4n3m4i1/Bode_Analyzer/App/FletApp/assets/Ari.png

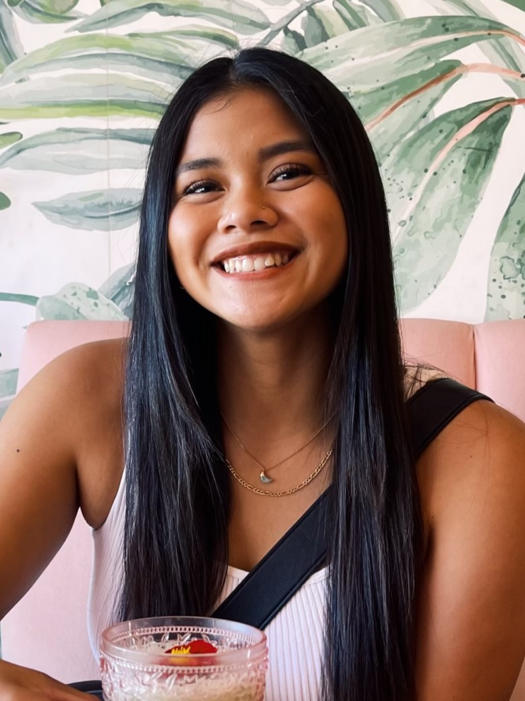
App/FletApp/assets/Ari.png
