4n3m4i1/Bode_Analyzer/App/FletApp/assets/AriBBTwo.png

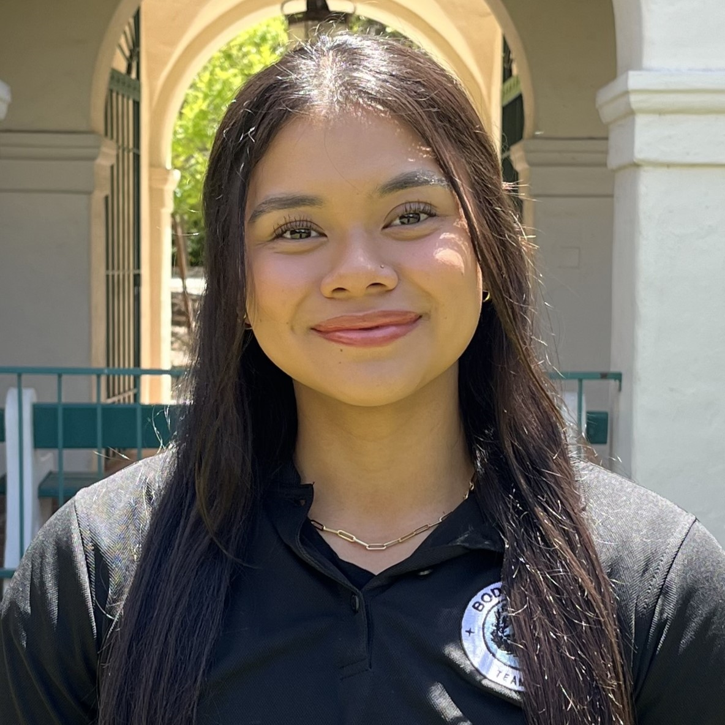
App/FletApp/assets/AriBBTwo.png
