4n3m4i1/Bode_Analyzer/App/FletApp/assets/ChristianFriends.png

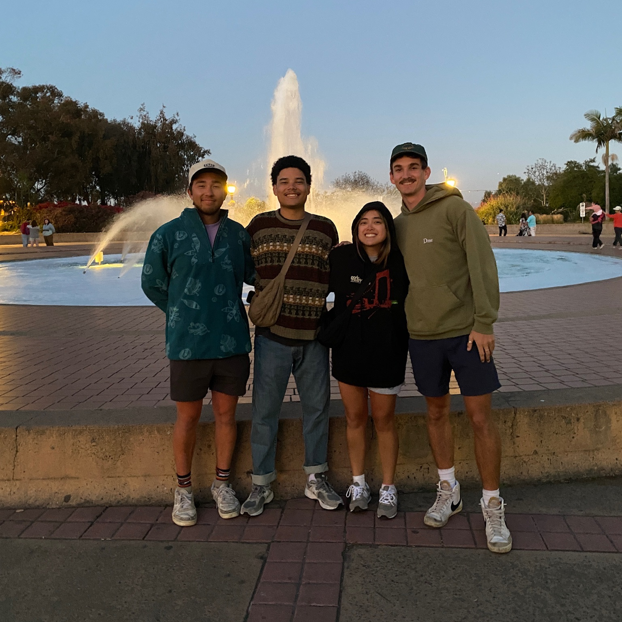
App/FletApp/assets/ChristianFriends.png
