4n3m4i1/Bode_Analyzer/App/FletApp/assets/JoshHobby.png

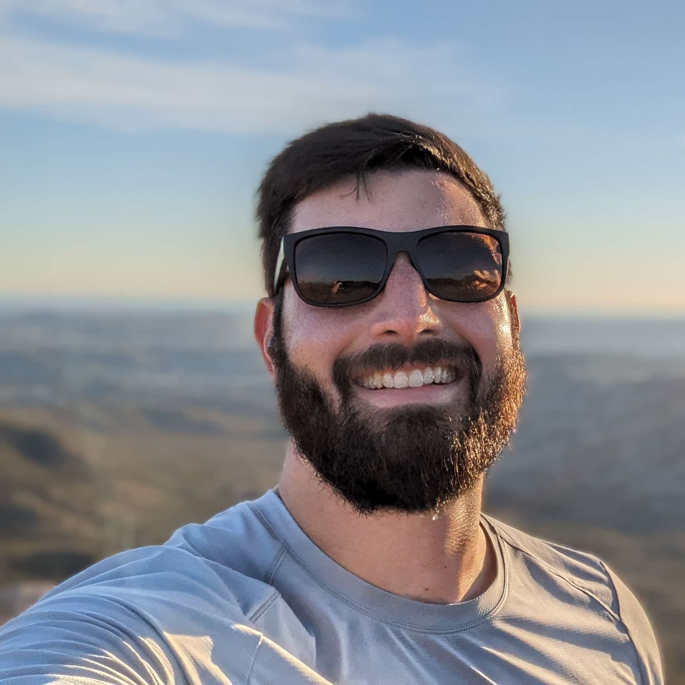
App/FletApp/assets/JoshHobby.png
