4n3m4i1/Bode_Analyzer/img/Ari.png

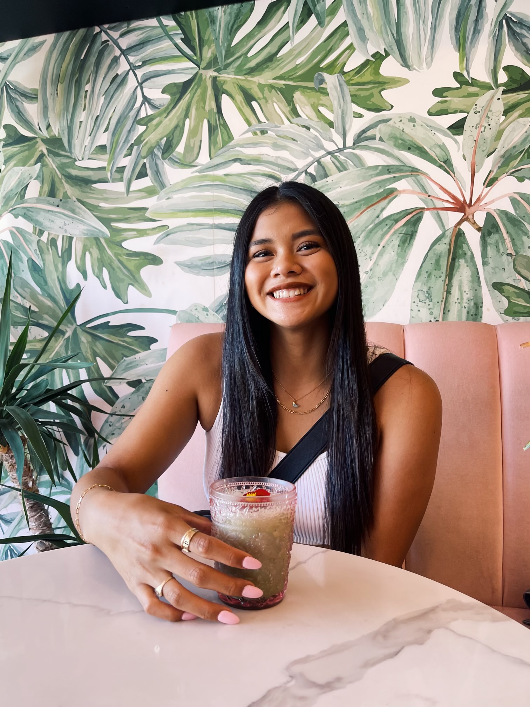
img/Ari.png
