4n3m4i1/Bode_Analyzer/Documentation/DSP/AdaptiveFilter/C_Adaptive_Filter_Test_Var_Taps/main.c

#include <stdio.h>
#include <stdlib.h>
#include <malloc.h>
#include <inttypes.h>
#include <math.h>

#define LIMIT_FOR_ERROR     1.0

#define DFL_ITERATIONS      256

#define DFL_BETA_RATE       0.005

#define ERR_AVE_LEN         8

uint32_t    print_options = 0;
#define CSV_OI4V_FMT        1u
#define TGT_VIDEO_FRAMES    1000

#define STARTING_TAP_TGT    32
#define MAX_TAP_TGT         1024

uint32_t    ideal_tap_num = 0;
uint32_t    adaptive_tap_num = 1024;
uint32_t    iterations = DFL_ITERATIONS;

// Different algorithms for H_HAT updates, leave all commented for DFL
//#define HALG_2        // DOESN'T WORK!!!!
//#define HALG_3        // DOESN'T WORK EVEN W /0 FIX!!
//#define HALG_4        // kinda a joke to try this one
//#define HALG_5

// Sorta kinda Box-Muller + Lazy Programming
double generate_awgn_sample(){
    double U1 = drand48();

    return sqrt(-2 * log(U1)) - 1.25;
}


// Simulate a DUT response HERE
double perform_fir(double *ideal_taps, double *idt_delay_line, double new_value, uint32_t len){
    double retval = 0;
    if(ideal_taps && idt_delay_line){
        idt_delay_line[0] = new_value;
        for(uint32_t n = 0; n < len; ++n) retval += ideal_taps[n] * idt_delay_line[n];
        for(uint32_t n = len - 1; n > 0; --n) idt_delay_line[n] = idt_delay_line[n - 1];
    }
    return retval;
}


void update_h_hat(double *h_hat_taps, double *idt_delay_line, double error, double beta_rate, uint32_t len){
    if(h_hat_taps && idt_delay_line){
#ifdef HALG_2
        for(uint32_t n = 0; n < len - 1; ++n){
            h_hat_taps[n + 1] = h_hat_taps[n] + beta_rate * (error * idt_delay_line[n]);
        }
#elif defined(HALG_3)
// Normalized
        for(uint32_t n = 0; n < len; ++n){
            if(!idt_delay_line[n]) idt_delay_line[n] += 1e-12;
            h_hat_taps[n] += (beta_rate * error) / (idt_delay_line[n]);
            printf("HE %lf\n",h_hat_taps[n]);
        }
#elif defined(HALG_4)
        for(uint32_t n = 0; n < len; ++n){
            h_hat_taps[n] -= beta_rate * (error * idt_delay_line[n]);
        }
#elif defined(HALG_5)
        for(uint32_t n = 0; n < len; ++n){
            h_hat_taps[n] += beta_rate * (2.0 * error * idt_delay_line[n]);
        }
#else
        for(uint32_t n = 0; n < len; ++n){
            h_hat_taps[n] += beta_rate * (error * idt_delay_line[n]);
        }
#endif
    }
}


void main(int argc, char **argv){
    if(argc > 1){
        iterations = strtoul(argv[1],NULL,10);
    }
    printf("Running %u samples of white noise through the system!\n", iterations);

    double beta = DFL_BETA_RATE;

    if(argc > 2){
        beta = strtod(argv[2],NULL);
    }

    printf("Beta adaptive rate: %lf\n",beta);


    FILE *printfp;
    if(argc > 3){
        print_options = CSV_OI4V_FMT;
        printf("Print History as Images: On!\n");
        printfp = fopen("adaptive_tap_frames.csv","w");
        fprintf(printfp,"%lu\n%.14lf\n", iterations, beta);
    }


    FILE *tapfp;
    tapfp = fopen("test_ideal_tap_weights.txt","r");

    double rval;

    while(fscanf(tapfp,"%lf",&rval) != EOF) ideal_tap_num += 1;
    printf("Number of Ideal Taps: %u\n",ideal_tap_num);
    rewind(tapfp);

    adaptive_tap_num = STARTING_TAP_TGT;

    // Establish skip count
    uint32_t frame_skip;
    if(print_options == CSV_OI4V_FMT){
        double ratio_t_2_i = iterations / TGT_VIDEO_FRAMES;
        if(iterations - TGT_VIDEO_FRAMES <= 0.5){
            frame_skip = (uint32_t)ratio_t_2_i;
        } else {
            frame_skip = (uint32_t) ratio_t_2_i + 1;
        }
        fprintf(printfp,"%lu\n",frame_skip);
    }



    double *ideal_taps = malloc(ideal_tap_num * sizeof(double));
    double *ideal_delay_line = malloc(ideal_tap_num * sizeof(double));

    double *adaptive_taps = malloc(MAX_TAP_TGT * sizeof(double));
    double *x = malloc(MAX_TAP_TGT * sizeof(double));

    double err;

    double *error_plot = malloc(iterations * sizeof(double));

    double *integral_error = malloc(iterations * sizeof(double));

    double error_accum = 0;

    double err_ave[ERR_AVE_LEN] = {1,1,1,1,1,1,1,1};

    double aved_err = 0;
    double old_aved_err = 0;
    double d_dt_err = 0;
    double d_dt_err_aved = 0;
    double d2_dt2_err = 0;
    double d2_dt2_err_aved = 0;

    if(ideal_taps && adaptive_taps && x && ideal_delay_line && error_plot && integral_error){
        
        for(uint32_t n = 0; n < ideal_tap_num; ++n){
            fscanf(tapfp,"%lf",&rval);
            ideal_taps[n] = rval;
            ideal_delay_line[n] = 0;
        }

        for(uint32_t n = 0; n < MAX_TAP_TGT; ++n){
            adaptive_taps[n] = 0;
            x[n] = 0;
        }

        // Save ideal taps
        if(print_options == CSV_OI4V_FMT){
            fprintf(printfp,"%lu\n",adaptive_tap_num);                  // print adaptive tap count
            fprintf(printfp,"%lu\n",ideal_tap_num);                     // Print number of ideal taps
            for(uint32_t q = 0; q < ideal_tap_num - 1; ++q){
                fprintf(printfp,"%.14lf,",ideal_taps[q]);
            }
            fprintf(printfp,"%.14lf\n",ideal_taps[ideal_tap_num - 1]);
        }

        
        // Run main sampling loop simulation
        for(uint32_t n = 0; n < iterations; ++n){
            double new_data = generate_awgn_sample();
            
            // Simulate a system under test's output given white noise input
            double target_sample_d = perform_fir(ideal_taps, ideal_delay_line, new_data, ideal_tap_num);

            // Run "internal" FIR structure
            double y_hat = perform_fir(adaptive_taps, x, new_data, adaptive_tap_num);
        
            // Determine output error
            err = target_sample_d - y_hat;
            
            // For statistics
            error_accum += err;
            error_plot[n] = err;


            for(uint32_t m = 1; m < ERR_AVE_LEN; ++m) err_ave[m] = err_ave[m - 1];
            err_ave[0] = err * err;

            aved_err = 0;
            for(uint32_t m = 0; m < ERR_AVE_LEN; ++m){
                aved_err += err_ave[m] * (1.0 / (double)ERR_AVE_LEN);
            }

            d_dt_err_aved = d_dt_err;
            d_dt_err = aved_err - old_aved_err;
            old_aved_err = aved_err;

            d2_dt2_err_aved = d2_dt2_err;
            d2_dt2_err = d_dt_err - d_dt_err_aved;

            //printf("%.14lf\n", aved_err);

            if(iterations == 5000){
                adaptive_tap_num *= 2;
                beta /= 2;
            } 


            // Iterate and reconfigure adaptive taps to correct for measured
            //  error.
            update_h_hat(adaptive_taps, x, err, beta, adaptive_tap_num);

            // Riemann sum taps, take difference
            for(uint32_t m = 0; m < adaptive_tap_num; ++m) integral_error[n] += adaptive_taps[m];
            for(uint32_t m = 0; m < ideal_tap_num; ++m) integral_error[n] -= ideal_taps[m];

            // Add new line for newest tap stuff
            if(print_options == CSV_OI4V_FMT){
                if(frame_skip){
                    if(!(n % frame_skip)){
                        for(uint32_t q = 0; q < adaptive_tap_num - 1; ++q){
                            fprintf(printfp,"%.14lf,",adaptive_taps[q]);
                        }
                        fprintf(printfp,"%.14lf\n",adaptive_taps[adaptive_tap_num - 1]);
                    }
                } else {
                    for(uint32_t q = 0; q < adaptive_tap_num - 1; ++q){
                        fprintf(printfp,"%.14lf,",adaptive_taps[q]);
                    }
                    fprintf(printfp,"%.14lf\n",adaptive_taps[adaptive_tap_num - 1]);
                }
            }
        }

        // Close file, turn into video
        if(print_options == CSV_OI4V_FMT){
            fclose(printfp);
        }

        double error_avg = fabs(error_accum / (double)iterations);

        if(error_avg > LIMIT_FOR_ERROR){
            printf("Failed to converge under error limit!! :^(\n");
        } else {
            printf("Final Adaptive Taps: %u\nFinal Beta: %.10lf\n",adaptive_tap_num,beta);
            printf("Completed simulation with an average error of:\n\t\t\t%.14lf\n",error_avg);
            printf("Final Integral Error:\t%.14lf\n",integral_error[iterations - 1]);    
        }
        


        // Setup output for:
        //      Ideal Taps
        //      h_hat
        //      e
        //      Tap error

        if(error_avg <= LIMIT_FOR_ERROR){
            FILE *fpo;
            fpo = fopen("ideal_tap_results.csv","w");
            fprintf(fpo,"IDX,IDEAL_TAP\n");
            for(uint32_t n = 0; n < ideal_tap_num; ++n){
                fprintf(fpo,"%u,%.14lf\n", n, ideal_taps[n]);
            }
            fclose(fpo);

            fpo = fopen("adaptive_tap_results.csv","w");
            fprintf(fpo,"IDX_ADAP,H_HAT\n");
            for(uint32_t n = 0; n < adaptive_tap_num; ++n){
                fprintf(fpo,"%u,%.14f\n",n,adaptive_taps[n]);
            }
            fclose(fpo);

            fpo = fopen("error_plot.csv","w");
            fprintf(fpo,"IDX,ERR,INT_ERR\n");
            for(uint32_t n = 0; n < iterations; ++n){
                fprintf(fpo,"%u,%.14lf,%.14lf\n",n,error_plot[n],integral_error[n]);
            }
            fclose(fpo);
        }
        

        free(ideal_taps);
        free(adaptive_taps);
        free(x);
        free(ideal_delay_line);
        free(error_plot);
        free(integral_error);
    } else {
        printf("Error allocating memory!\n");
    }
    fclose(tapfp);
}
