4n3m4i1/Bode_Analyzer/src/tests/feature_tests/PIO_ADS7253/ADS_CONSTANTS.h

#ifndef ADSCONSTANTS_h
#define ADSCONSTANTS_h

#define ADS_PIO_MAIN_SM 0
#define ADS_PIO_SDOA_SM 1
#define ADS_PIO_SDOB_SM 2

enum ADS7253_REGISTER_ADDRESSES {
    ADS7253_NOP,
    ADS7253_REFDAC_A_READ,
    ADS7253_REFDAC_B_READ,
    ADS7253_CFR_READ,
    ADS7253_CFR_WRITE = (1 << 3),
    ADS7253_REFDAC_A_WRITE,
    ADS7253_REFDAC_B_WRITE
};


enum ADS7253_CFR_BITS {
    ADS7253_CFR_ZERO_0,
    ADS7253_CFR_ZERO_1,
    ADS7253_CFR_ZERO_2,
    ADS7253_CFR_ZERO_3,
    ADS7253_CFR_RD_DATA_FMT,
    ADS7253_CFR_STANDBY,
    ADS7253_CFR_REF_SEL,
    ADS7253_CFR_INM_SEL,
    ADS7253_CFR_ZERO_4,
    ADS7253_CFR_INPUT_RANGE,
    ADS7253_CFR_RD_DATA_LINES,
    ADS7253_CFR_RD_CLK_MODE,
    ADS7253_CFR_ADDR0,
    ADS7253_CFR_ADDR1,
    ADS7253_CFR_ZERO_5,
    ADS7253_CFR_WRITE_READ
};

#define ADS7253_SET_SINGLE_SDO  (1u << ADS7253_CFR_RD_DATA_LINES)
#define ADS7253_SET_16_CLK_MODE (1u << ADS7253_CFR_RD_CLK_MODE)
#define ADS7253_USE_INTERNAL_REFERENCE  (1u << ADS7253_CFR_REF_SEL)
#define ADS7253_2X_REFDAC       (1u << ADS7253_CFR_INPUT_RANGE)

enum ADS7253_REFDAC_BITS {
    ADS7253_REFDAC_ZERO_0,
    ADS7253_REFDAC_ZERO_1,
    ADS7253_REFDAC_ZERO_2,
    ADS7253_REFDAC_D_0,
    ADS7253_REFDAC_D_1,
    ADS7253_REFDAC_D_2,
    ADS7253_REFDAC_D_3,
    ADS7253_REFDAC_D_4,
    ADS7253_REFDAC_D_5,
    ADS7253_REFDAC_D_6,
    ADS7253_REFDAC_D_7,
    ADS7253_REFDAC_ADDR0,
    ADS7253_REFDAC_ADDR1,
    ADS7253_REFDAC_ZERO_3,
    ADS7253_REFDAC_WRITE_READ
};

/*
    Modes:
        Single 32   -> 0 << 1 | 0
        Single 16   -> 1 << 1 | 0
        Dual 32     -> 0 << 1 | 1
        Dual 16     -> 1 << 1 | 1
*/
enum ADS7253_SAMPLING_MODES {
    ADS7253_32_CLK_MODE,
    ADS7253_16_CLK_MODE
};  

enum ADS7253_SPI_MODES {
    ADS7253_SINGLE_SDO,
    ADS7253_DUAL_SDO
};

#define ADS7253_SINGLE_32_MODE_         ((ADS7253_32_CLK_MODE << 1) | (ADS7253_SINGLE_SDO))
#define ADS7253_SINGLE_16_MODE_         ((ADS7253_16_CLK_MODE << 1) | (ADS7253_SINGLE_SDO))
#define ADS7253_DUAL_32_MODE_           ((ADS7253_32_CLK_MODE << 1) | (ADS7253_DUAL_SDO))
#define ADS7253_DUAL_16_MODE_           ((ADS7253_16_CLK_MODE << 1) | (ADS7253_DUAL_SDO))

#define ADS7253_MIN_SINGLE_SDO_16_CLKS  32
#define ADS7253_MIN_SINGLE_SDO_32_CLKS  48
#define ADS7253_MIN_DUAL_SDO_16_CLKS    16
#define ADS7253_MIN_DUAL_SDO_32_CLKS    32

#define ADS7253_CMD(_operation, _data)  ((uint16_t)(_operation << 12) | _data)

#endif
